Saitejas21/piku-desk-robot/variants/cat/cad/cat_back.step

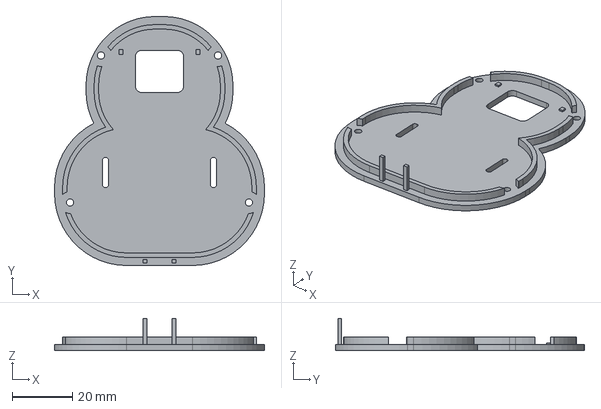
[picture p28: CAD file, 2026-09-13]
variants/cat/cad/cat_back.step
70.0 x 83.0 x 10.7 mm
