Saitejas21/piku-desk-robot/variants/cat/cad/cat_shell_review.step

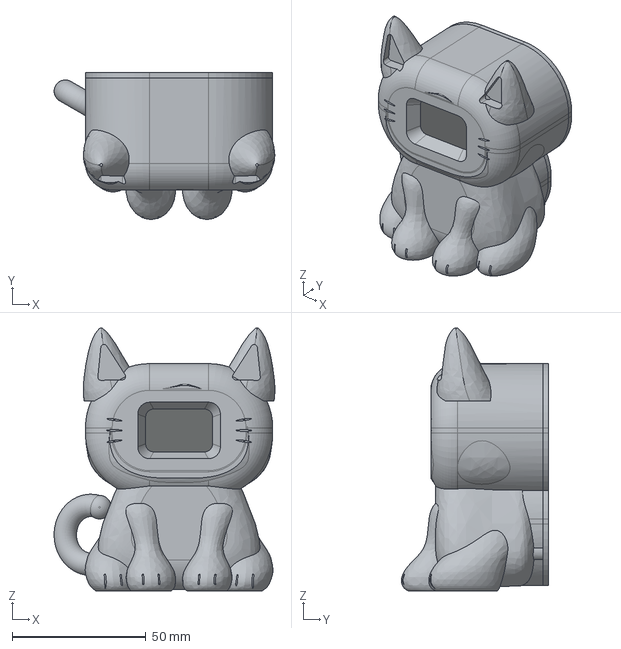
[picture p29: CAD file, 2026-09-13]
variants/cat/cad/cat_shell_review.step
82.5 x 55.0 x 98.3 mm
