Saitejas21/piku-desk-robot/variants/cat/cad/cat_inside.step

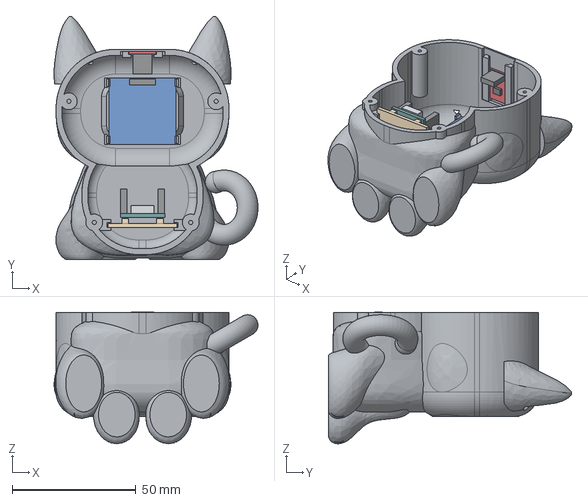
[picture p30: CAD file, 2026-09-13]
variants/cat/cad/cat_inside.step
82.5 x 98.3 x 53.2 mm
