Saitejas21/piku-desk-robot/variants/otter/cad/otter_back.step

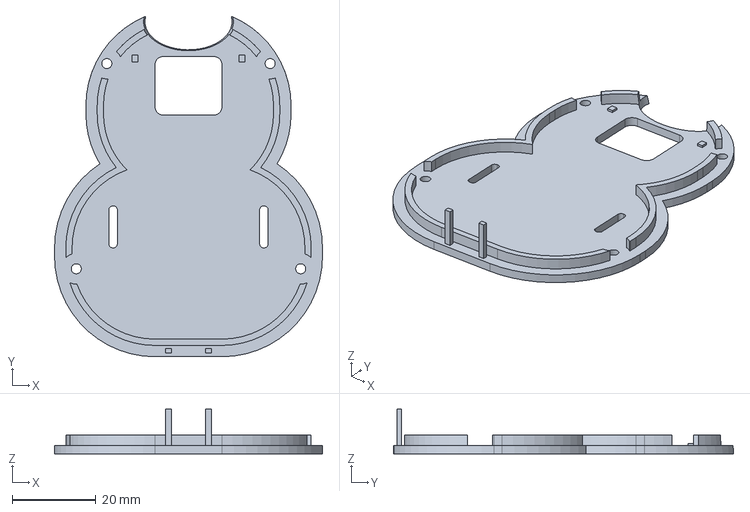
[picture p31: CAD file, 2026-09-13]
variants/otter/cad/otter_back.step
64.0 x 81.3 x 10.7 mm
